thingSoC/TSOC_PSoC4L/TSOC_PSoC4L/documentation/pinout/TSOC_PSoC4L_pinout.jpg

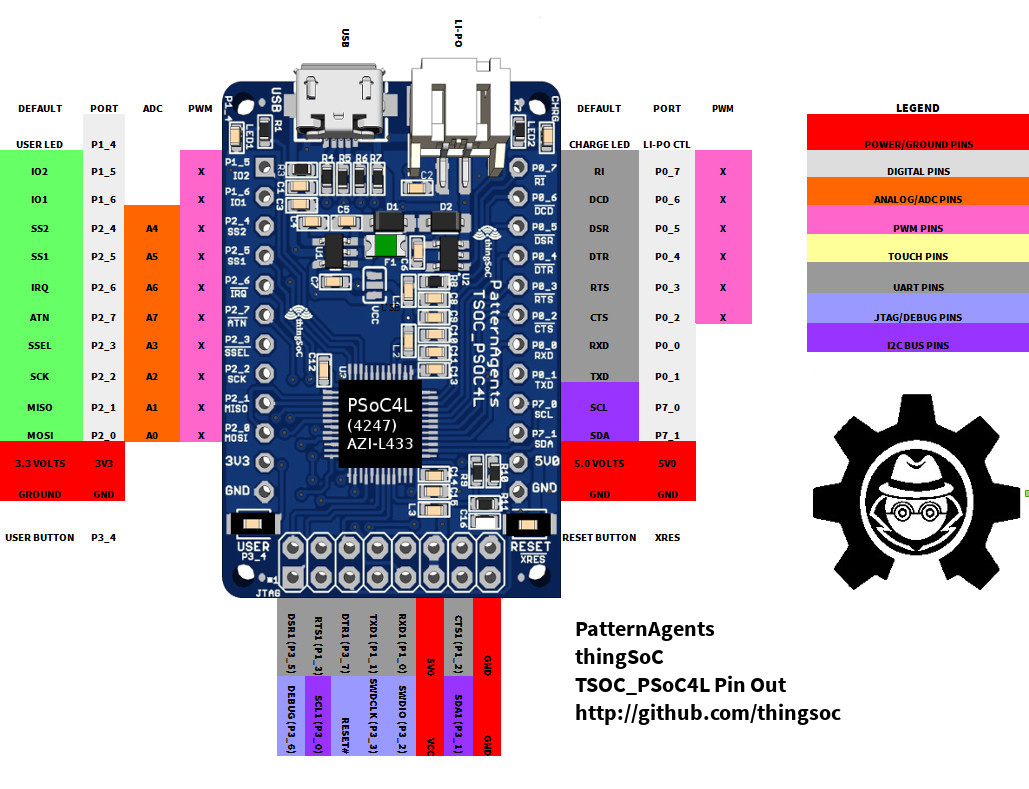
TSOC_PSoC4L/documentation/pinout/TSOC_PSoC4L_pinout.jpg
