thingSoC/TSOC_PSoC4L/TSOC_PSoC4L/eagleUp/eagleUp_TSOC_PSoC4L_board_top.jpg

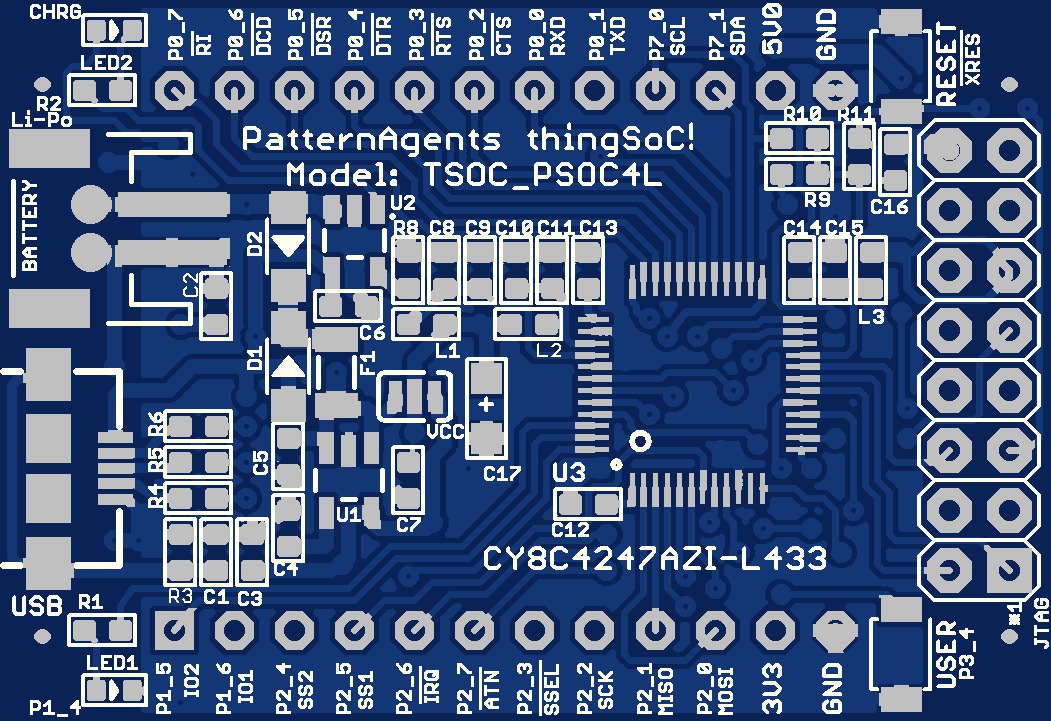
TSOC_PSoC4L/eagleUp/eagleUp_TSOC_PSoC4L_board_top.jpg
