thingSoC/TSOC_PSoC4L/TSOC_PSoC4L/images/product/TSOC_PSoC4L_4up.png

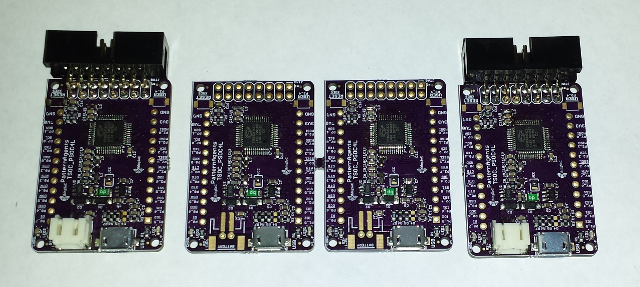
TSOC_PSoC4L/images/product/TSOC_PSoC4L_4up.png
