thingSoC/TSOC_PSoC4L/TSOC_PSoC4L/images/product/TSOC_PSoC4L_bagged.jpg

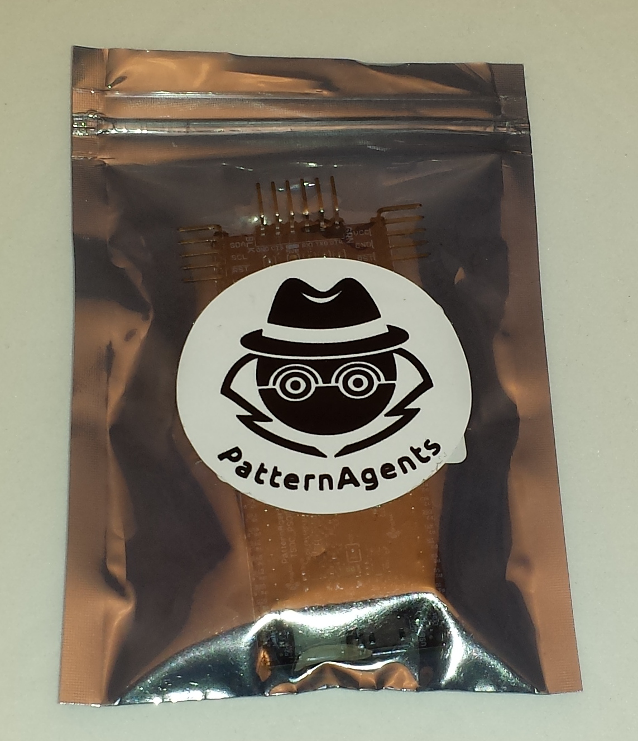
TSOC_PSoC4L/images/product/TSOC_PSoC4L_bagged.jpg
