thingSoC/TSOC_PSoC4L/TSOC_PSoC4L/images/product/TSOC_PSoC4L_bottom.jpg

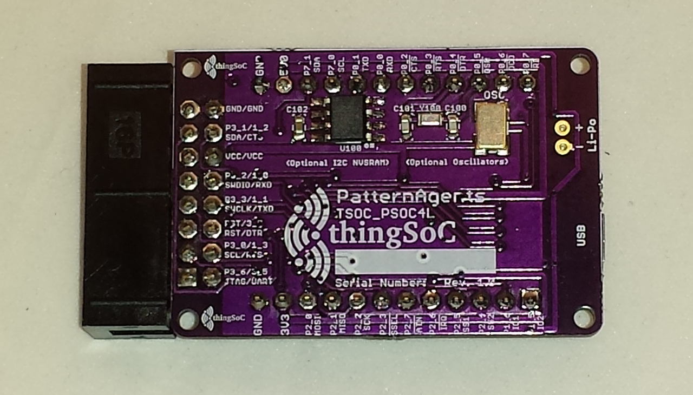
TSOC_PSoC4L/images/product/TSOC_PSoC4L_bottom.jpg
