thingSoC/TSOC_PSoC4L/TSOC_PSoC4L/images/product/TSOC_PSoC4L_JTAG_adapter.jpg

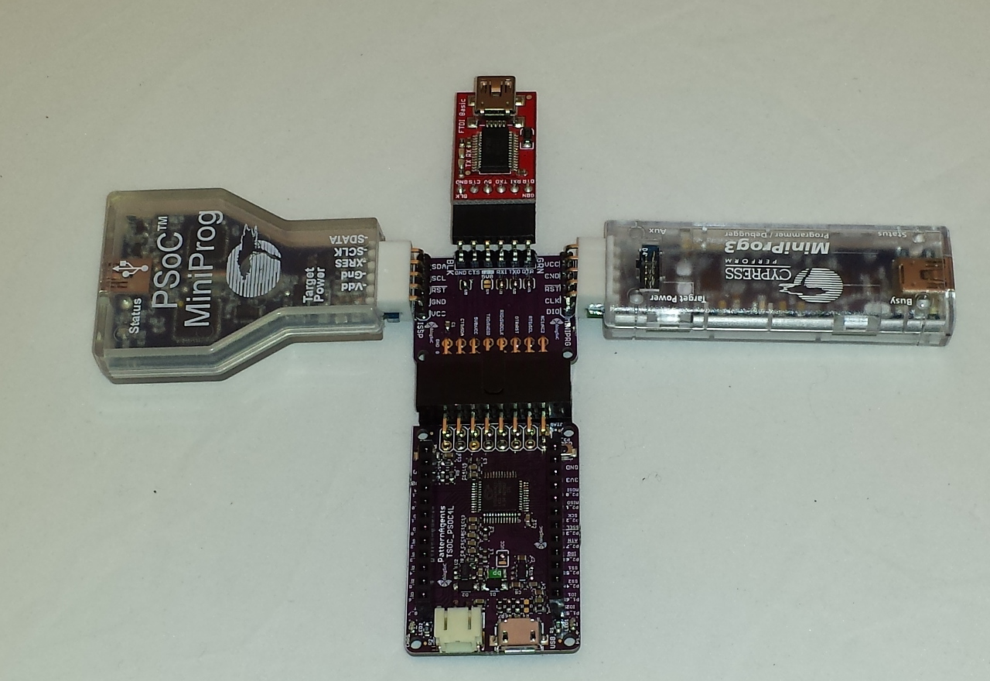
TSOC_PSoC4L/images/product/TSOC_PSoC4L_JTAG_adapter.jpg
