thingSoC/TSOC_PSoC4L/TSOC_PSoC4L/images/product/TSOC_PSoC4L_pop.png

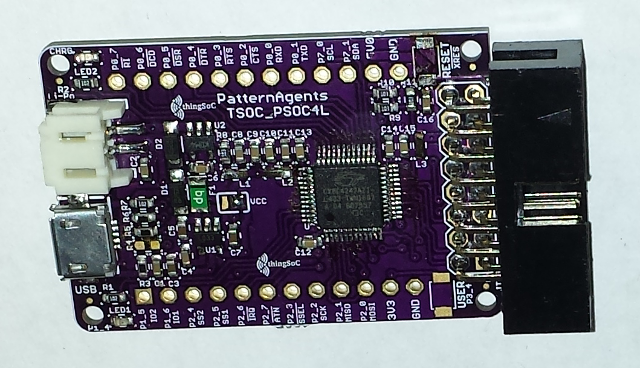
TSOC_PSoC4L/images/product/TSOC_PSoC4L_pop.png
