thingSoC/TSOC_PSoC4L/TSOC_PSoC4L/images/product/TSOC_PSoC4L_weather.png

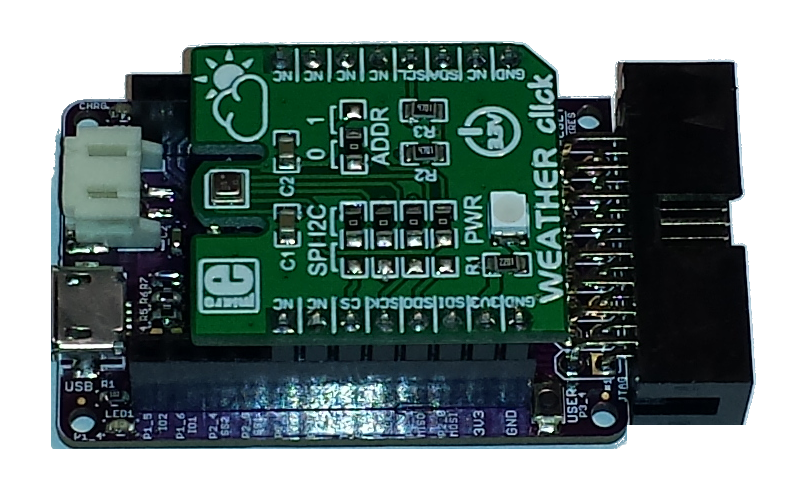
TSOC_PSoC4L/images/product/TSOC_PSoC4L_weather.png
