thingSoC/TSOC_PSoC4L/TSOC_PSoC4L/images/product/with_ESP-32S.png

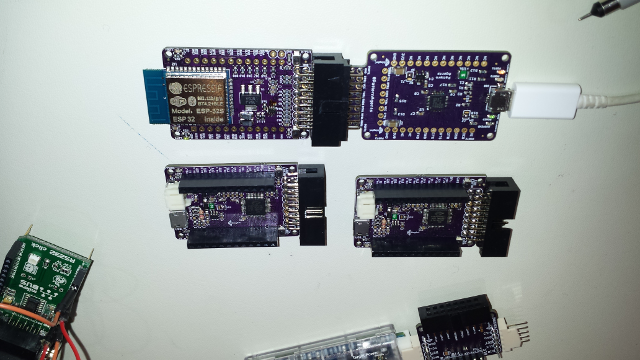
TSOC_PSoC4L/images/product/with_ESP-32S.png
