thingSoC/TSOC_PSoC4L/TSOC_PSoC4L/images/TSOC_PSoC4L_iso.jpg

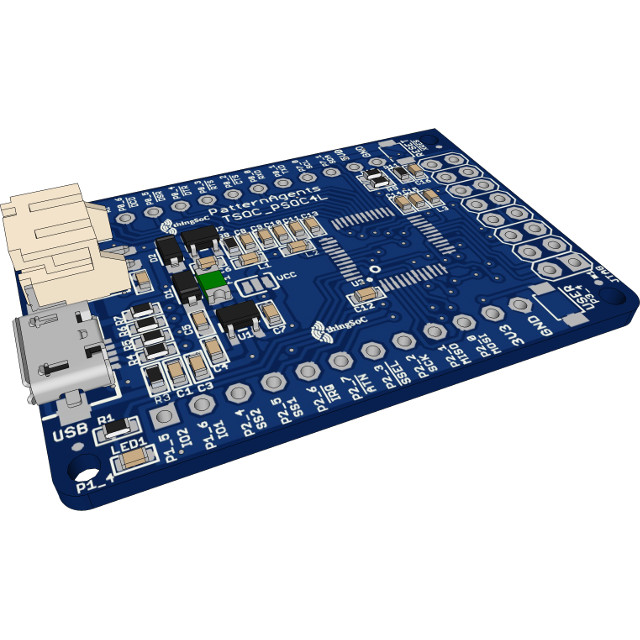
TSOC_PSoC4L/images/TSOC_PSoC4L_iso.jpg
